DavidCalles/Laser-line-3D-Scanner/Description_Images/Up_platform.png

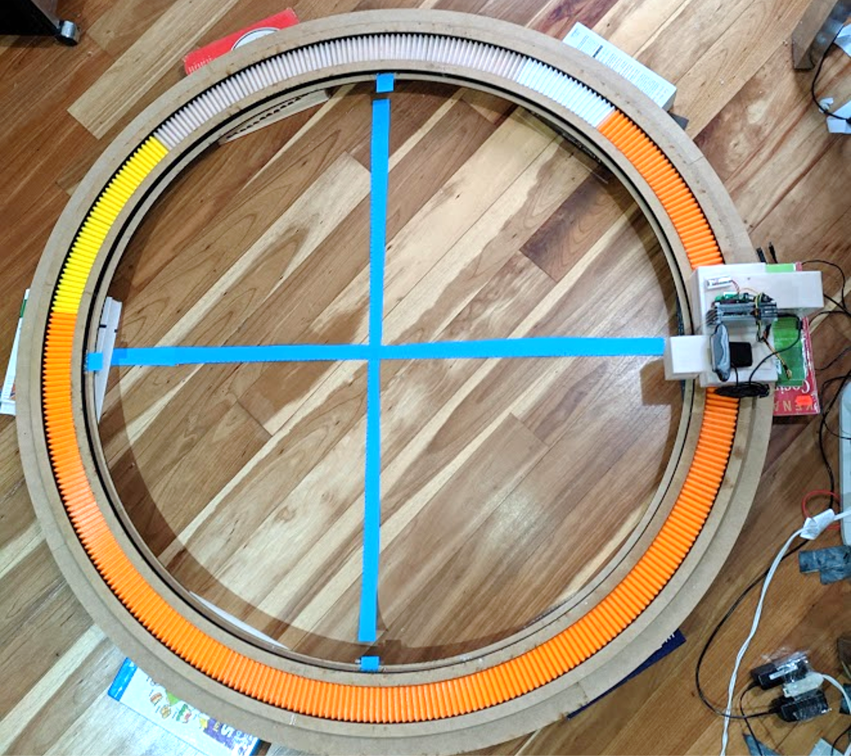
Description_Images/Up_platform.png
