DavidCalles/Laser-line-3D-Scanner/PCB/PCB_real.PNG

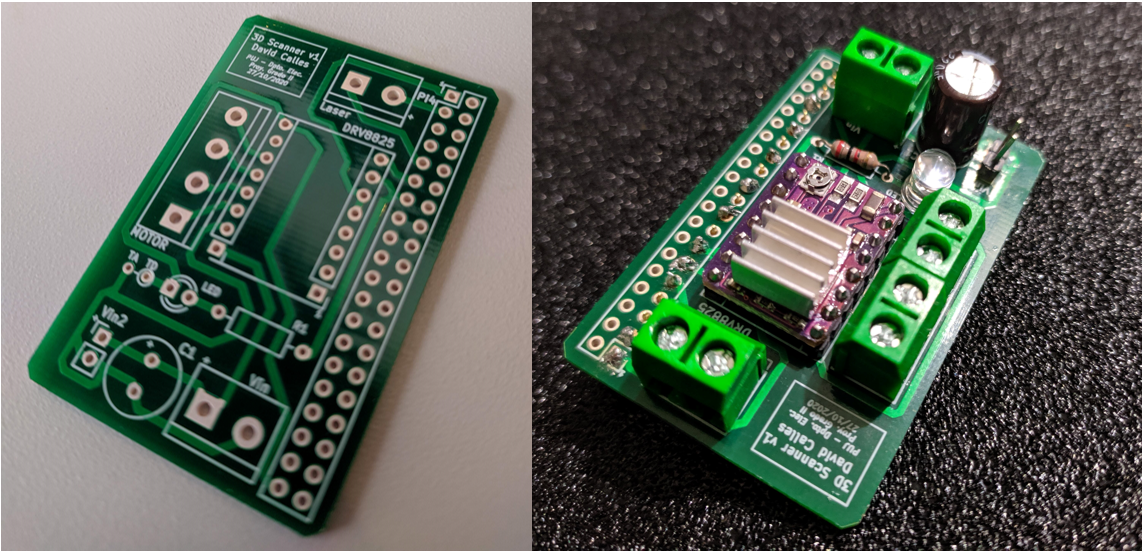
PCB/PCB_real.PNG
