DavidCalles/Laser-line-3D-Scanner/PCB/PCB_virtual.PNG

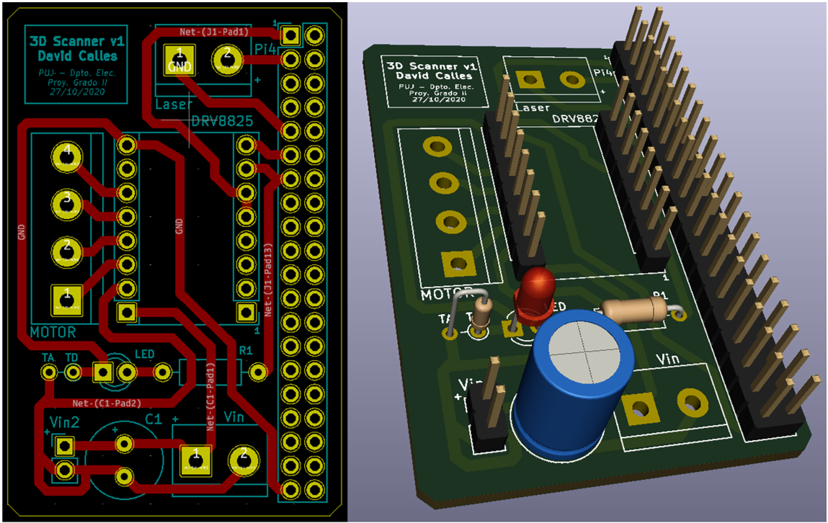
PCB/PCB_virtual.PNG
