DavidCalles/Laser-line-3D-Scanner/Camera_Calibration_Image_Set/Image_92.png

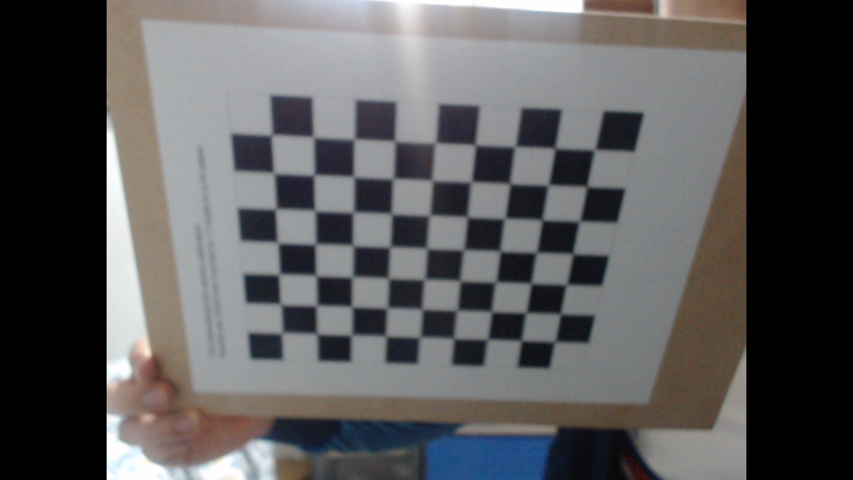
Camera_Calibration_Image_Set/Image_92.png
