DavidCalles/Laser-line-3D-Scanner/Camera_Calibration_Image_Set/Image_94.png

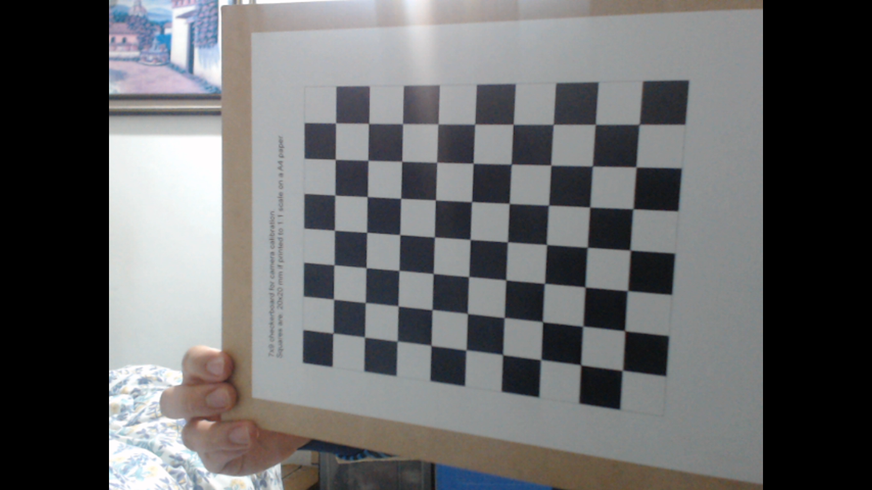
Camera_Calibration_Image_Set/Image_94.png
