DavidCalles/Laser-line-3D-Scanner/Center_Calibration_Set/CenterA.png

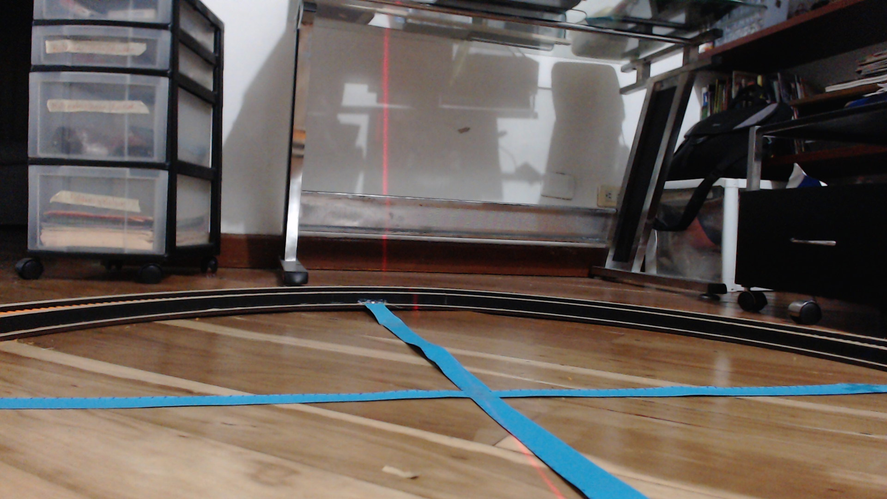
Center_Calibration_Set/CenterA.png
